Bread80/CPC_Keyboards/Keyswitch_CPC464_SMT/Images/FittedFront-pcbway.jpg

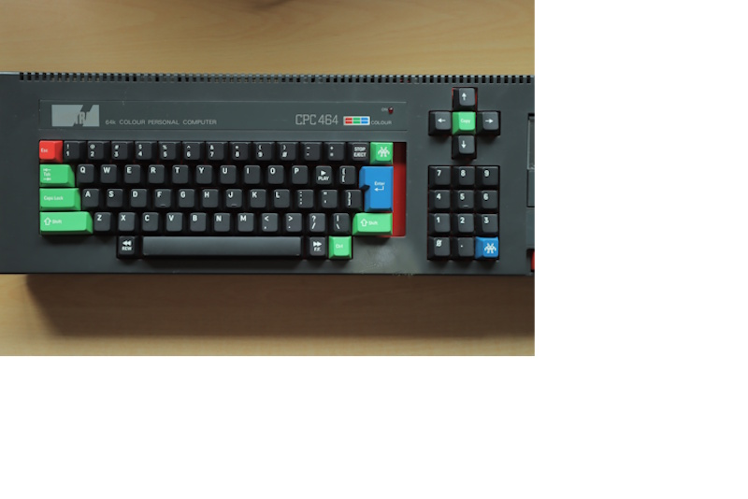
Keyswitch_CPC464_SMT/Images/FittedFront-pcbway.jpg
