Bread80/CPC_Keyboards/Keyswitch_CPC464_SMT/Images/FittedReverse-pcbway.jpg

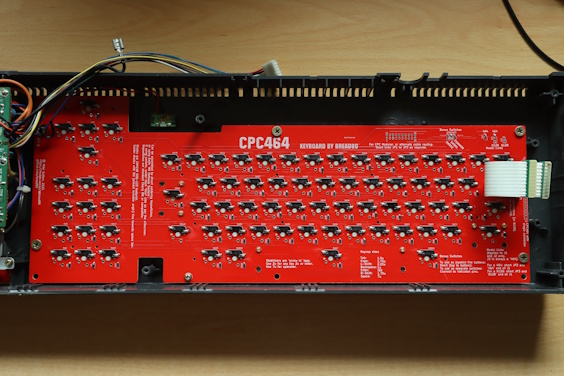
Keyswitch_CPC464_SMT/Images/FittedReverse-pcbway.jpg
