Bread80/CPC_Keyboards/Keyswitch_CPC464_SMT/Images/IMG_3361.JPG

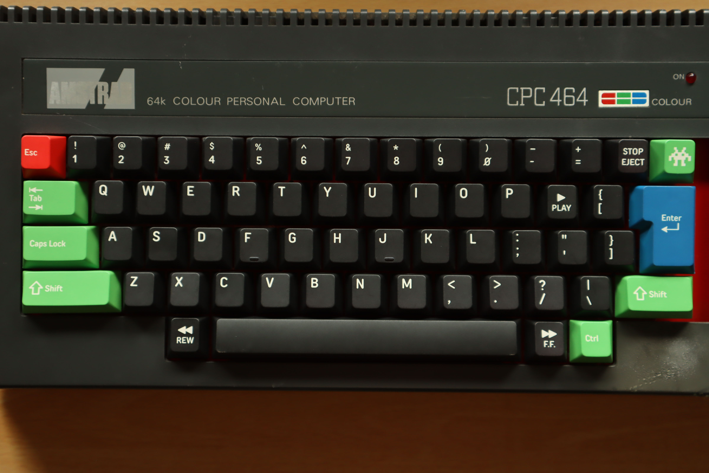
Keyswitch_CPC464_SMT/Images/IMG_3361.JPG
