Bread80/CPC_Keyboards/Keyswitch_CPC464_SMT/Images/RearDetail-pcbway.jpg

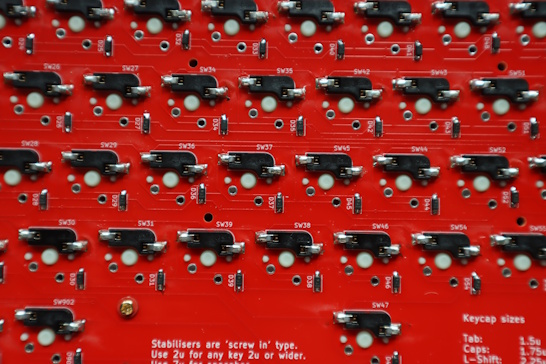
Keyswitch_CPC464_SMT/Images/RearDetail-pcbway.jpg
