Bread80/CPC_Keyboards/Keyswitch_CPC464_SMT/Images/RearDetail-small.jpg

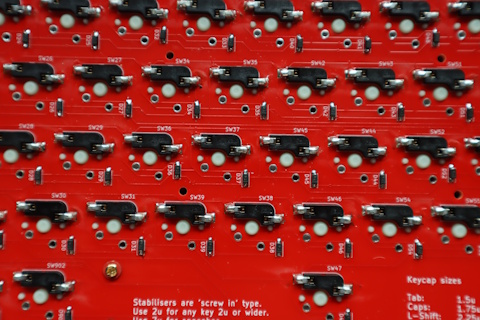
Keyswitch_CPC464_SMT/Images/RearDetail-small.jpg
